makerfx/allison-chase-guardian/images/pixel-ring-mockups/pixel-ring-mockup-03.png

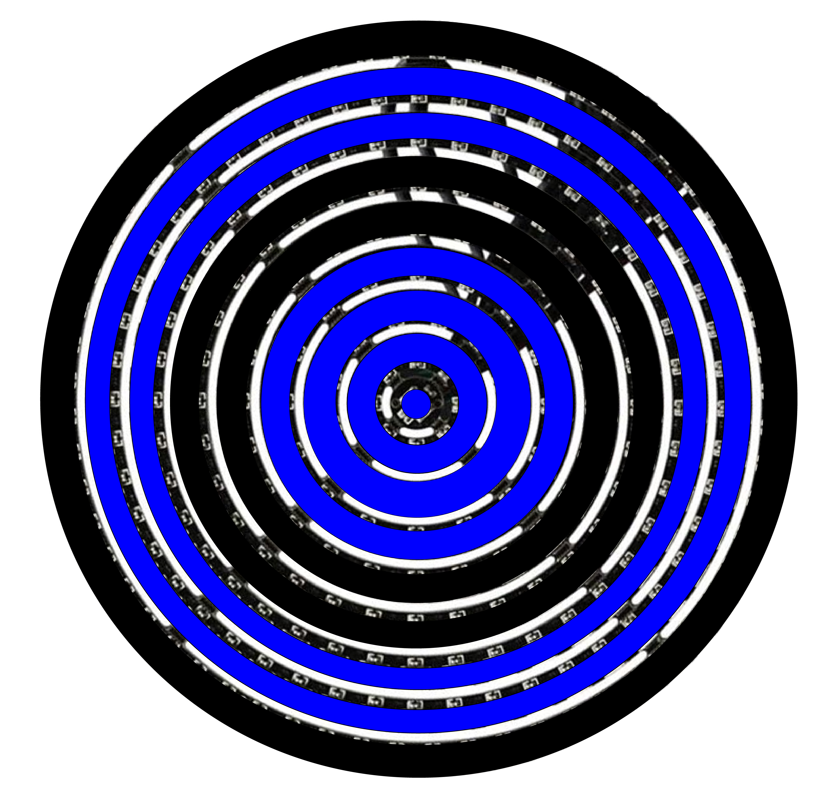
images/pixel-ring-mockups/pixel-ring-mockup-03.png
